46nori/Z80Atmega128/schematics/KiCad/ExtIO_sch.kicad_sch

## KiCad design schematics/KiCad/ExtIO_sch.kicad_sch (2023-12-28, an earlier design)

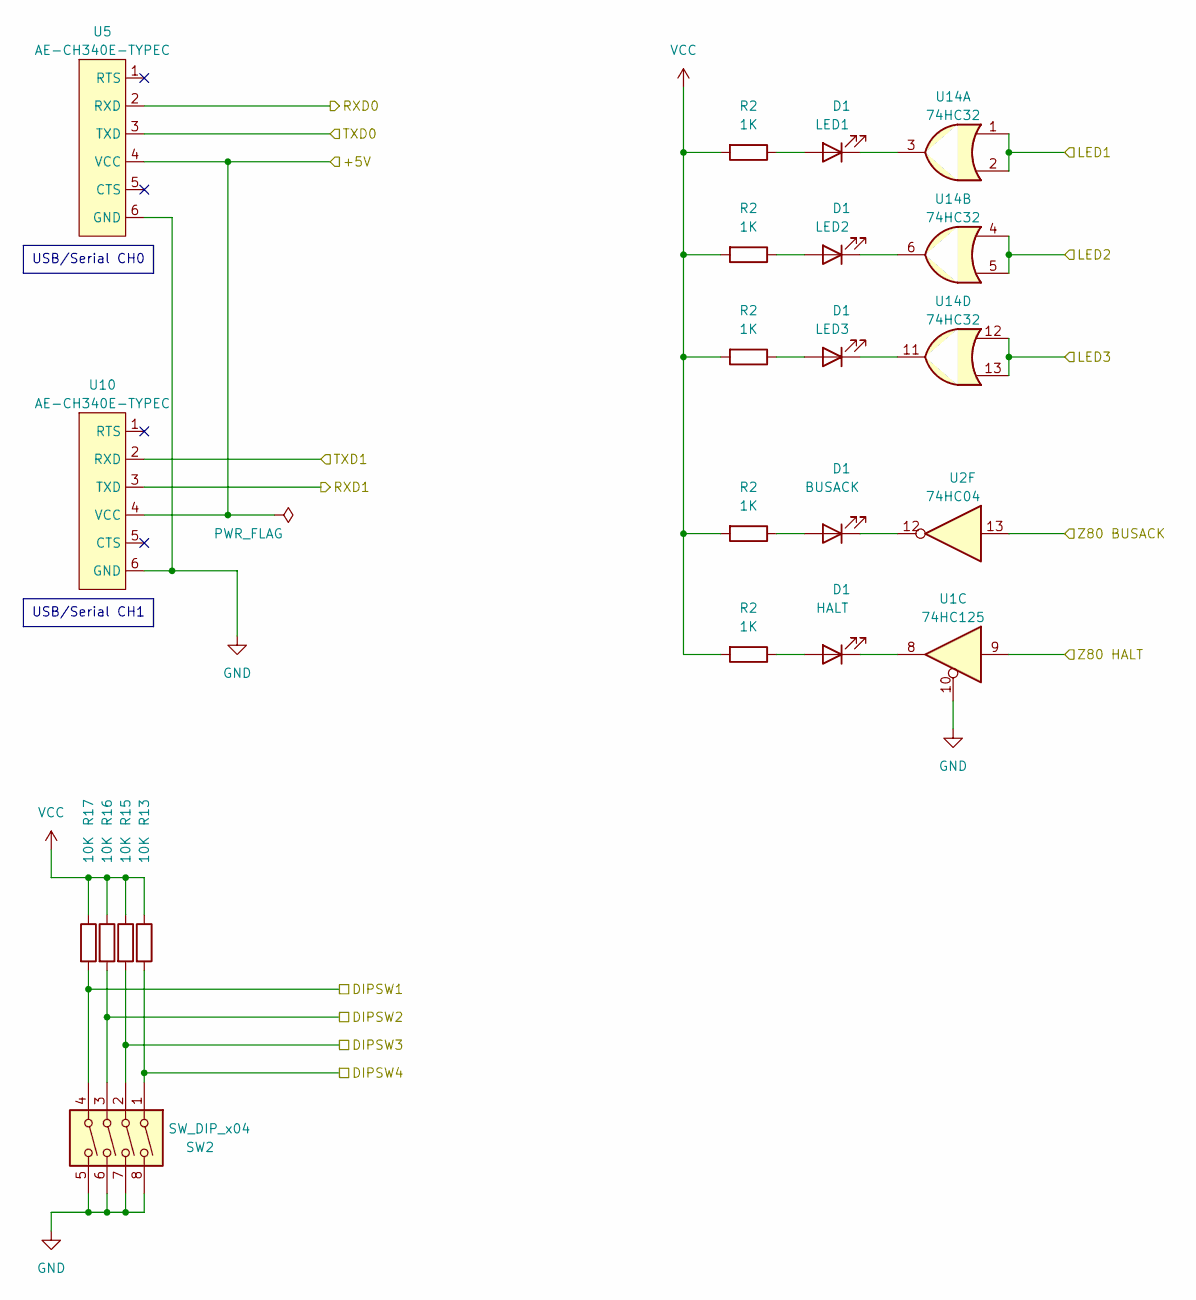
[picture p24: schematic ExtIO_sch.kicad_sch]

Parts:
D1: LED2; LED_D3.0mm
R2: 1K; R_Axial_DIN0204_L3.6mm_D1.6mm_P7.62mm_Horizontal
R13, R15, R16, R17: 10K; R_Axial_DIN0204_L3.6mm_D1.6mm_P7.62mm_Horizontal
SW2: SW_DIP_x04; SW_DIP_SPSTx04_Slide_9.78x12.34mm_W7.62mm_P2.54mm
U1: 74HC125; DIP-14_W7.62mm_Socket
U2: 74HC04; DIP-14_W7.62mm_Socket
U5, U10: AE-CH340E-TYPEC; PinHeader_1x06_P2.54mm_Vertical
U14: 74HC32; DIP-14_W7.62mm_Socket

Connections:
+5V: U5.4 (VCC), U10.4 (VCC)
DIPSW1: R17.2, SW2.4
DIPSW2: R16.2, SW2.3
DIPSW3: R15.2, SW2.2
DIPSW4: R13.2, SW2.1
GND: SW2.5, SW2.6, SW2.7, SW2.8, U1.10, U5.6 (GND), U10.6 (GND)
LED1: U14.1, U14.2
LED2: U14.4, U14.5
LED3: U14.12, U14.13
unnamed: D1.1 (K), U1.8, U2.12, U14.3, U14.6, U14.11
unnamed: D1.2 (A), R2.1
RXD0: U5.2 (RXD)
RXD1: U10.3 (TXD)
TXD0: U5.3 (TXD)
TXD1: U10.2 (RXD)
VCC: R2.2, R13.1, R15.1, R16.1, R17.1
Z80 BUSACK: U2.13
Z80 HALT: U1.9

Notes on the sheet:
USB/Serial CH1
USB/Serial CH0
