46nori/Z80Atmega128/schematics/KiCad/Reset.kicad_sch

## KiCad design schematics/KiCad/Reset.kicad_sch (2023-12-28, an earlier design)

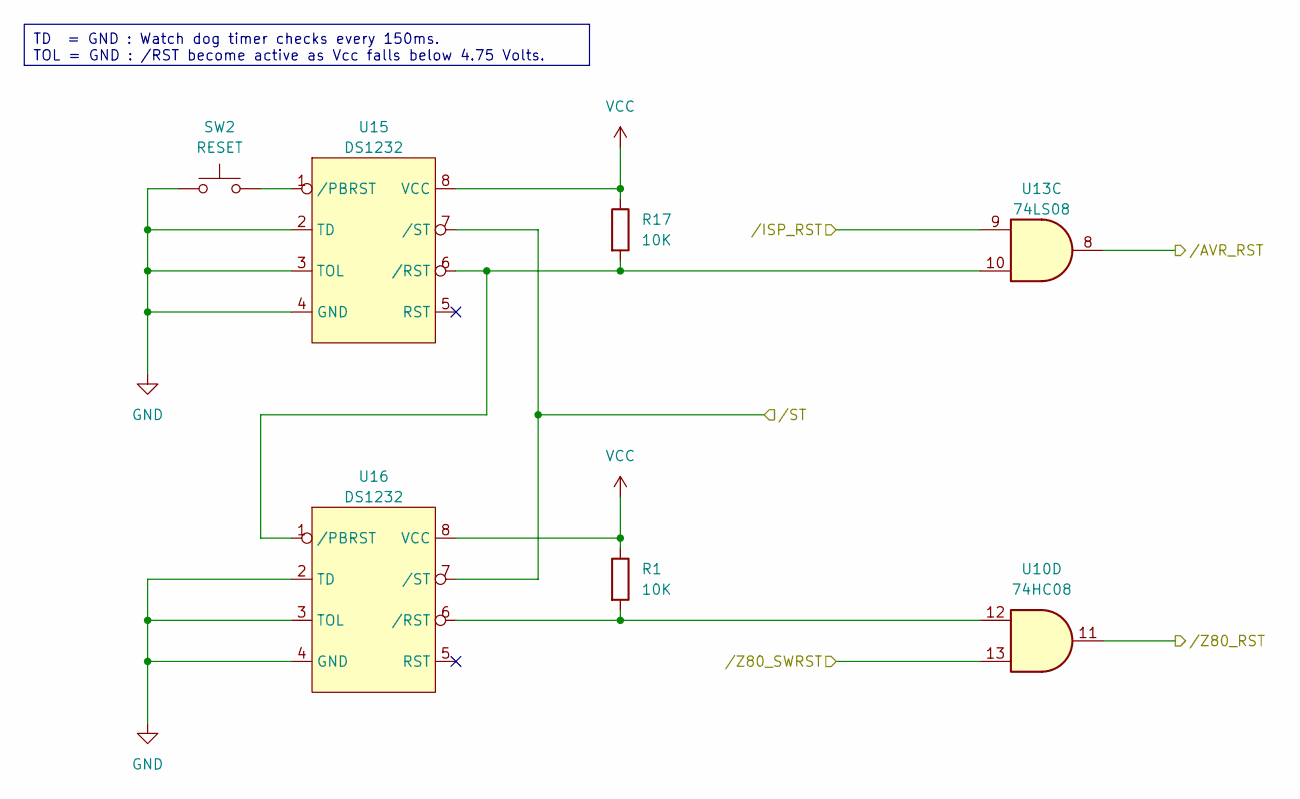
[picture p25: schematic Reset.kicad_sch]

Parts:
R1, R17: 10K; R_Axial_DIN0204_L3.6mm_D1.6mm_P7.62mm_Horizontal
SW2: RESET; SW_PUSH_6mm_H7.3mm
U10: 74HC08; DIP-14_W7.62mm_Socket
U13: 74LS08; DIP-14_W7.62mm_Socket
U15, U16: DS1232; DIP-8_W7.62mm

Connections:
GND: SW2.1, U15.2 (TD), U15.3 (TOL), U15.4 (GND), U16.2 (TD), U16.3 (TOL), U16.4 (GND)
unnamed: R1.2, U10.12, U16.6 (/RST)
unnamed: R17.2, U13.10, U15.6 (/RST), U16.1 (/PBRST)
unnamed: SW2.2, U15.1 (/PBRST)
VCC: R1.1, R17.1, U15.8 (VCC), U16.8 (VCC)
/AVR_RST: U13.8
/ISP_RST: U13.9
/ST: U15.7 (/ST), U16.7 (/ST)
/Z80_RST: U10.11
/Z80_SWRST: U10.13

Notes on the sheet:
TD = GND : Watch dog timer checks every 150ms. TOL = GND : /RST become active as Vcc falls below 4.75 Volts.
