46nori/Z80Atmega128/schematics/KiCad/SD_Card.kicad_sch

## KiCad design schematics/KiCad/SD_Card.kicad_sch (2023-12-28, an earlier design)

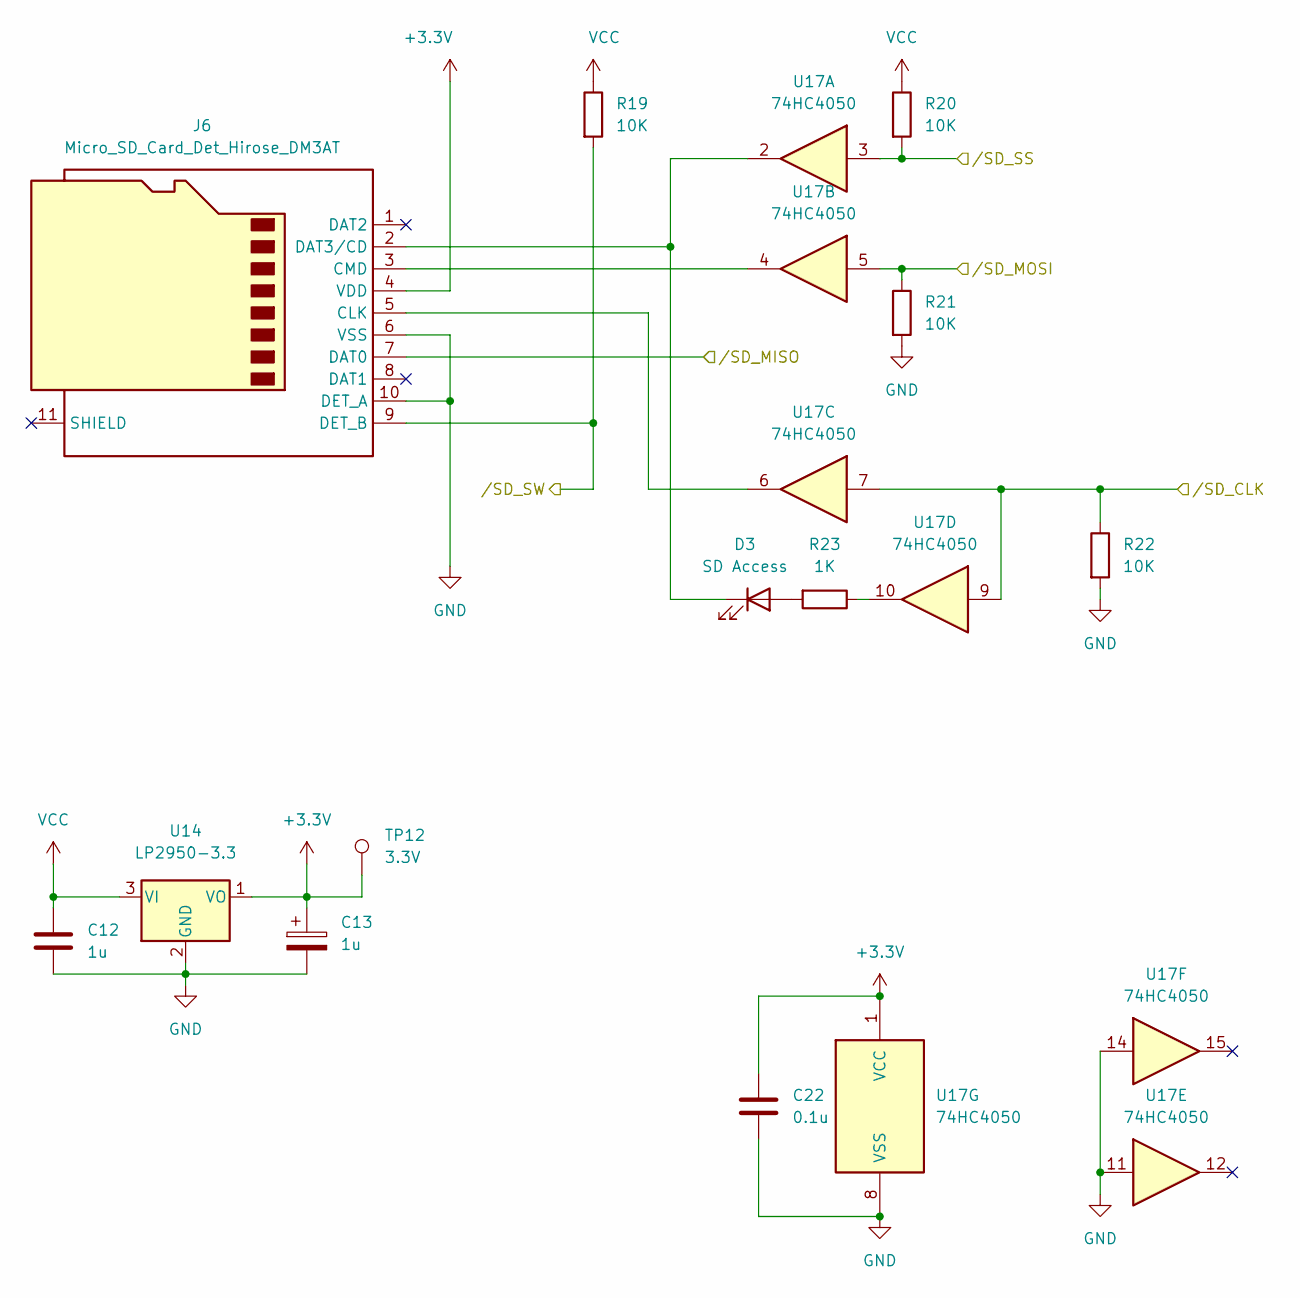
[picture p26: schematic SD_Card.kicad_sch]

Parts:
C12, C13: 1u; CP_Radial_Tantal_D5.0mm_P2.50mm
C22: 0.1u; C_Disc_D3.8mm_W2.6mm_P2.50mm
D3: SD Access; LED_D3.0mm
J6: Micro_SD_Card_Det_Hirose_DM3AT; microSD_HC_Hirose_DM3AT-SF-PEJM5
R19, R20, R21, R22: 10K; R_Axial_DIN0204_L3.6mm_D1.6mm_P7.62mm_Horizontal
R23: 1K; R_Axial_DIN0204_L3.6mm_D1.6mm_P7.62mm_Horizontal
TP12: 3.3V; TestPoint_Loop_D2.50mm_Drill1.0mm
U14: LP2950-3.3; TO-92_Inline
U17: 74HC4050; DIP-16_W7.62mm_Socket

Connections:
+3.3V: C13.1, C22.1, J6.4 (VDD), TP12.1, U14.1 (VO), U17.1 (VCC)
GND: C12.2, C13.2, C22.2, J6.6 (VSS), J6.10 (DET_A), R21.2, R22.2, U14.2 (GND), U17.8 (VSS), U17.11, U17.14
unnamed: D3.1 (K), J6.2 (DAT3/CD), U17.2
unnamed: D3.2 (A), R23.2
unnamed: J6.3 (CMD), U17.4
unnamed: J6.5 (CLK), U17.6
unnamed: R23.1, U17.10
VCC: C12.1, R19.1, R20.1, U14.3 (VI)
/SD_CLK: R22.1, U17.7, U17.9
/SD_MISO: J6.7 (DAT0)
/SD_MOSI: R21.1, U17.5
/SD_SS: R20.2, U17.3
/SD_SW: J6.9 (DET_B), R19.2
