46nori/Z80Atmega128/schematics/KiCad/Z80ATmega128.kicad_sch

## KiCad design schematics/KiCad/Z80ATmega128.kicad_sch (2023-12-28, an earlier design)

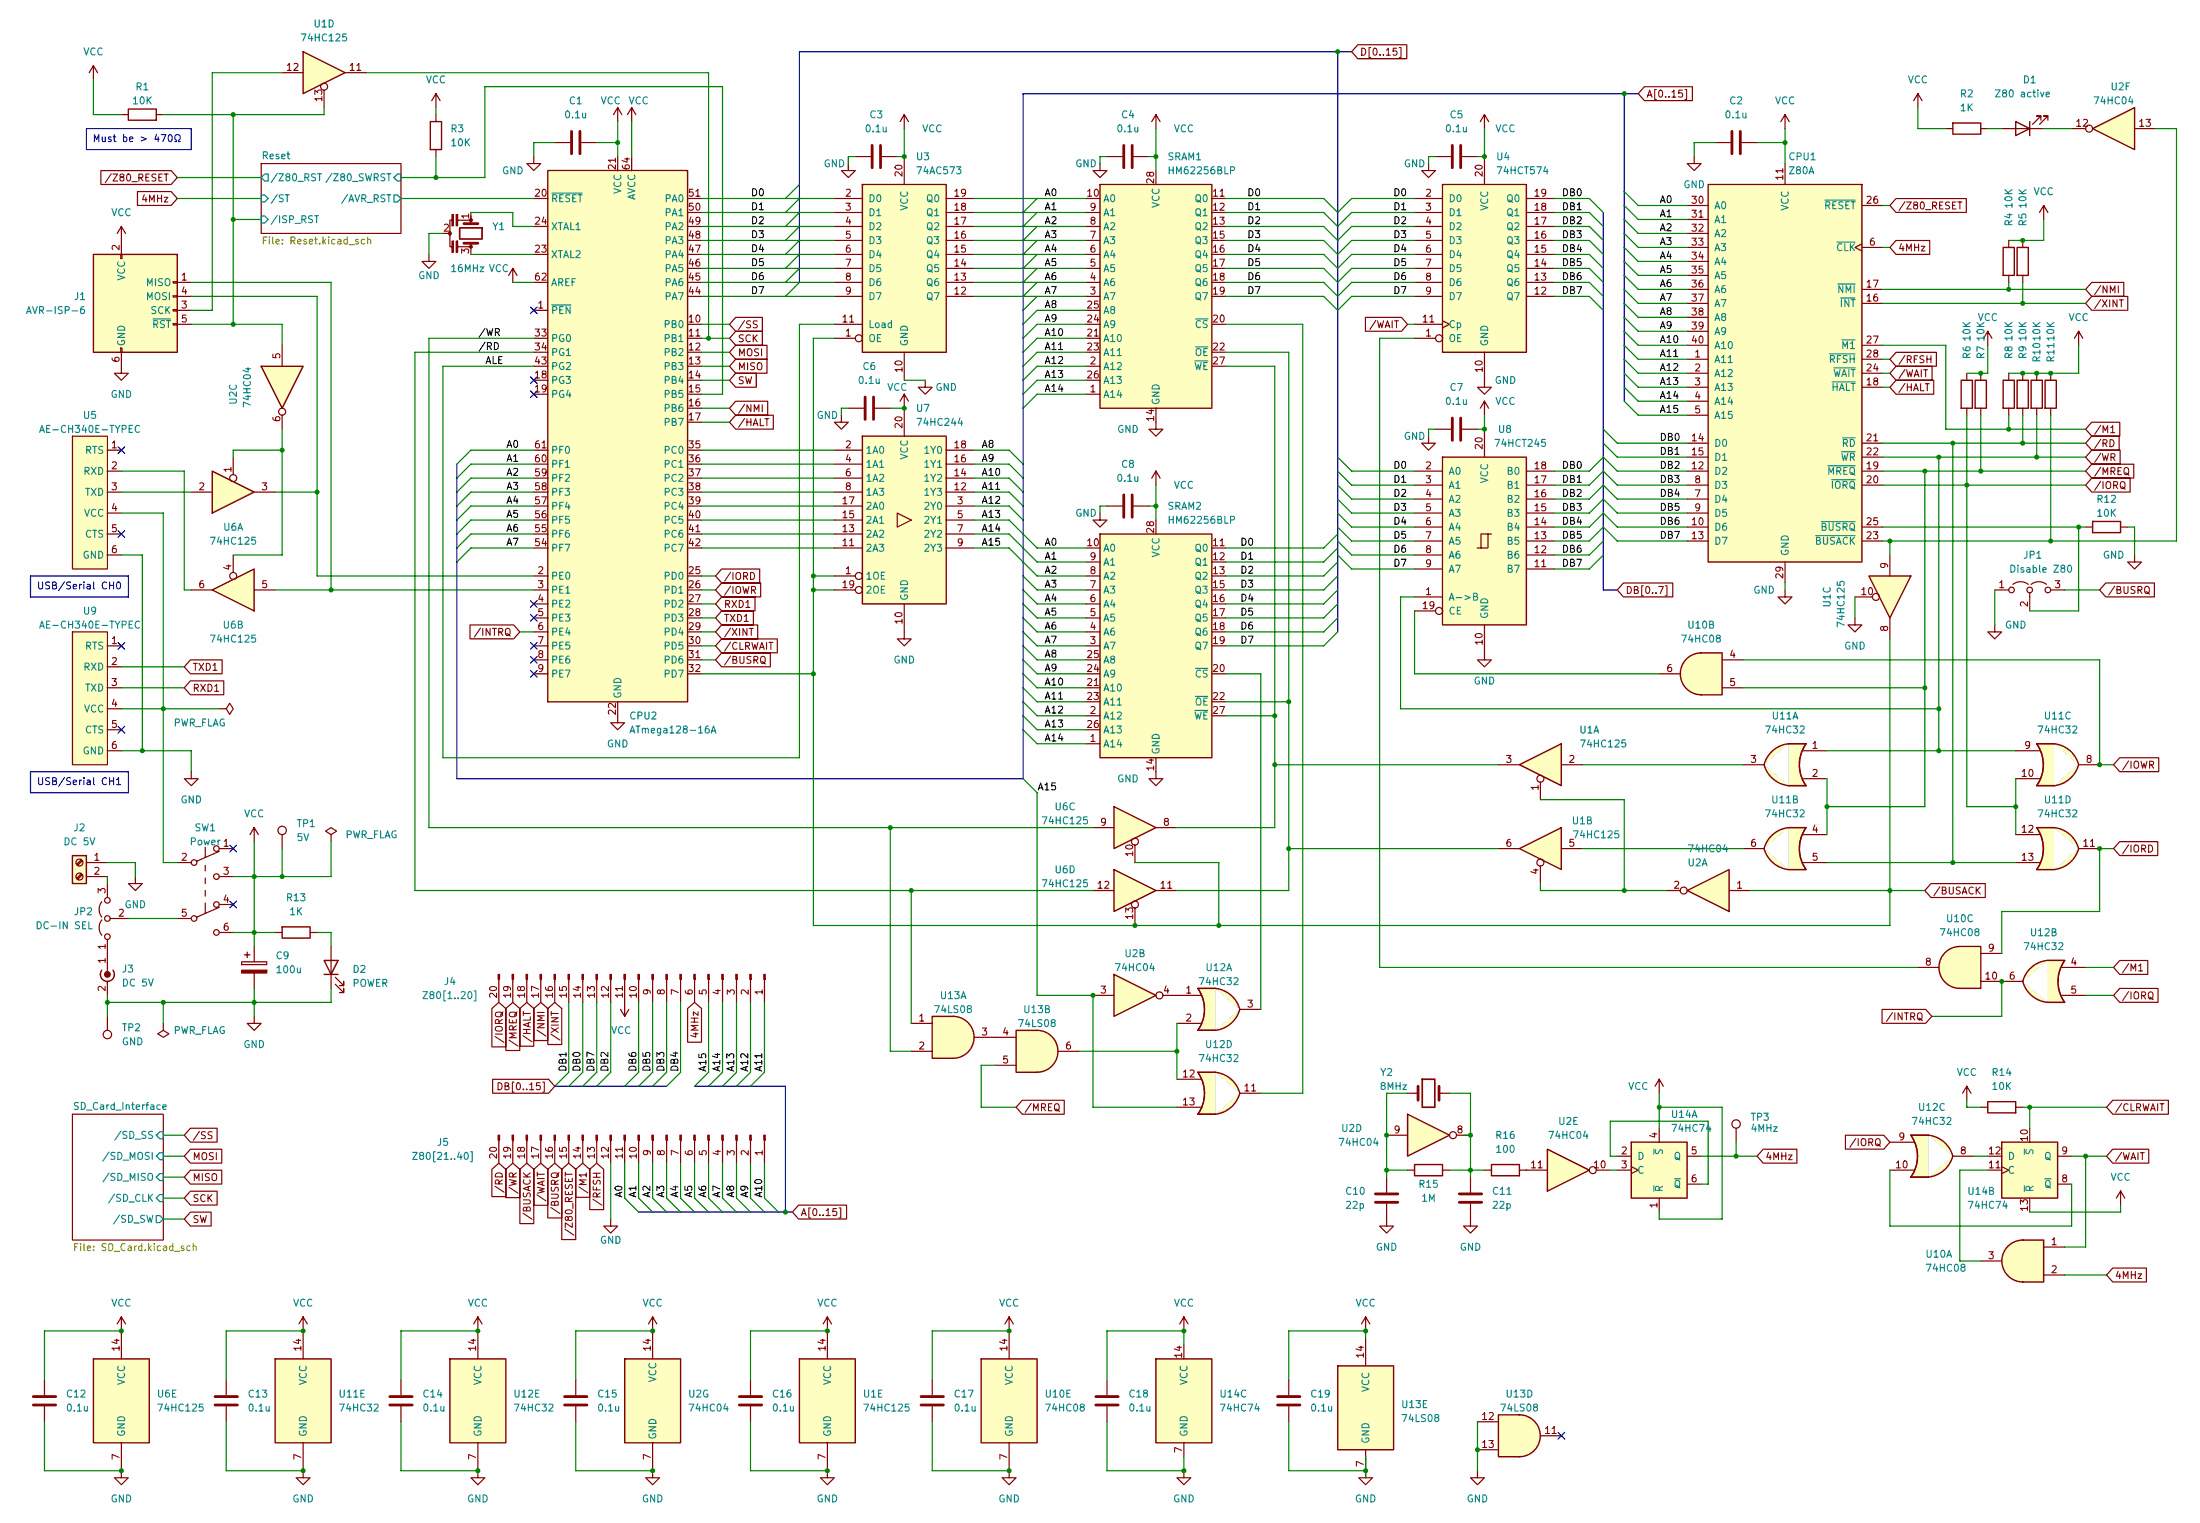
[picture p27: schematic Z80ATmega128.kicad_sch]

Parts:
C1, C2, C3, C4, C5, C6, C7, C8, C12, C13, C14, C15, C16, C17, C18, C19: 0.1u; C_Disc_D3.8mm_W2.6mm_P2.50mm
C9: 100u; CP_Radial_Tantal_D5.0mm_P2.50mm
C10, C11: 22p; C_Disc_D3.8mm_W2.6mm_P2.50mm
CPU1: Z80A; DIP-40_W15.24mm_Socket
CPU2: ATmega128-16A; TQFP-64_14x14mm_P0.8mm
D1: Z80 active; LED_D3.0mm
D2: POWER; LED_D3.0mm
J1: AVR-ISP-6; PinHeader_2x03_P2.54mm_Vertical
J2: DC 5V; TerminalBlock_Altech_AK300-2_P5.00mm
J3: DC 5V; BarrelJack_Horizontal
J4: Z80[1..20]; PinHeader_1x20_P2.54mm_Vertical
J5: Z80[21..40]; PinHeader_1x20_P2.54mm_Vertical
JP1: Disable Z80; PinHeader_1x03_P2.54mm_Vertical
JP2: DC-IN SEL; PinHeader_1x03_P2.54mm_Vertical
R1, R3, R4, R5, R6, R7, R8, R9, R10, R11, R12, R14: 10K; R_Axial_DIN0204_L3.6mm_D1.6mm_P7.62mm_Horizontal
R2, R13: 1K; R_Axial_DIN0204_L3.6mm_D1.6mm_P7.62mm_Horizontal
R15: 1M; R_Axial_DIN0204_L3.6mm_D1.6mm_P7.62mm_Horizontal
R16: 100; R_Axial_DIN0204_L3.6mm_D1.6mm_P7.62mm_Horizontal
SRAM1, SRAM2: HM62256BLP; DIP-28_W15.24mm_Socket
SW1: Power
TP1: 5V; TestPoint_Loop_D2.50mm_Drill1.0mm
TP2: GND; TestPoint_Loop_D2.50mm_Drill1.0mm
TP3: 4MHz; TestPoint_Loop_D2.50mm_Drill1.0mm
U1, U6: 74HC125; DIP-14_W7.62mm_Socket
U2: 74HC04; DIP-14_W7.62mm_Socket
U3: 74AC573; DIP-20_W7.62mm_Socket
U4: 74HCT574; DIP-20_W7.62mm_Socket
U5, U9: AE-CH340E-TYPEC; PinHeader_1x06_P2.54mm_Vertical
U7: 74HC244; DIP-20_W7.62mm_Socket
U8: 74HCT245; DIP-20_W7.62mm_Socket
U10: 74HC08; DIP-14_W7.62mm_Socket
U11, U12: 74HC32; DIP-14_W7.62mm_Socket
U13: 74LS08; DIP-14_W7.62mm_Socket
U14: 74HC74; DIP-14_W7.62mm_Socket
Y1: 16MHz; Resonator_Murata_CSTLSxxxX-3Pin_W5.5mm_H3.0mm
Y2: 8MHz; Crystal_HC18-U_Vertical

Connections:
4MHz: CPU1.6 (~CLK), J4.6, TP3.1, U10.2, U14.5 (Q)
A0: CPU1.30 (A0), CPU2.61 (PF0), J5.11, SRAM1.10 (A0), SRAM2.10 (A0), U3.19 (Q0)
A1: CPU1.31 (A1), CPU2.60 (PF1), J5.10, SRAM1.9 (A1), SRAM2.9 (A1), U3.18 (Q1)
A2: CPU1.32 (A2), CPU2.59 (PF2), J5.9, SRAM1.8 (A2), SRAM2.8 (A2), U3.17 (Q2)
A3: CPU1.33 (A3), CPU2.58 (PF3), J5.8, SRAM1.7 (A3), SRAM2.7 (A3), U3.16 (Q3)
A4: CPU1.34 (A4), CPU2.57 (PF4), J5.7, SRAM1.6 (A4), SRAM2.6 (A4), U3.15 (Q4)
A5: CPU1.35 (A5), CPU2.56 (PF5), J5.6, SRAM1.5 (A5), SRAM2.5 (A5), U3.14 (Q5)
A6: CPU1.36 (A6), CPU2.55 (PF6), J5.5, SRAM1.4 (A6), SRAM2.4 (A6), U3.13 (Q6)
A7: CPU1.37 (A7), CPU2.54 (PF7), J5.4, SRAM1.3 (A7), SRAM2.3 (A7), U3.12 (Q7)
A8: CPU1.38 (A8), J5.3, SRAM1.25 (A8), SRAM2.25 (A8), U7.18 (1Y0)
A9: CPU1.39 (A9), J5.2, SRAM1.24 (A9), SRAM2.24 (A9), U7.16 (1Y1)
A10: CPU1.40 (A10), J5.1, SRAM1.21 (A10), SRAM2.21 (A10), U7.14 (1Y2)
A11: CPU1.1 (A11), J4.1, SRAM1.23 (A11), SRAM2.23 (A11), U7.12 (1Y3)
A12: CPU1.2 (A12), J4.2, SRAM1.2 (A12), SRAM2.2 (A12), U7.3 (2Y0)
A13: CPU1.3 (A13), J4.3, SRAM1.26 (A13), SRAM2.26 (A13), U7.5 (2Y1)
A14: CPU1.4 (A14), J4.4, SRAM1.1 (A14), SRAM2.1 (A14), U7.7 (2Y2)
A15: CPU1.5 (A15), J4.5, U2.3, U7.9 (2Y3), U12.13
ALE: CPU2.43 (PG2), U3.11 (Load)
D0: CPU2.51 (PA0), SRAM1.11 (Q0), SRAM2.11 (Q0), U3.2 (D0), U4.2 (D0), U8.2 (A0)
D1: CPU2.50 (PA1), SRAM1.12 (Q1), SRAM2.12 (Q1), U3.3 (D1), U4.3 (D1), U8.3 (A1)
D2: CPU2.49 (PA2), SRAM1.13 (Q2), SRAM2.13 (Q2), U3.4 (D2), U4.4 (D2), U8.4 (A2)
D3: CPU2.48 (PA3), SRAM1.15 (Q3), SRAM2.15 (Q3), U3.5 (D3), U4.5 (D3), U8.5 (A3)
D4: CPU2.47 (PA4), SRAM1.16 (Q4), SRAM2.16 (Q4), U3.6 (D4), U4.6 (D4), U8.6 (A4)
D5: CPU2.46 (PA5), SRAM1.17 (Q5), SRAM2.17 (Q5), U3.7 (D5), U4.7 (D5), U8.7 (A5)
D6: CPU2.45 (PA6), SRAM1.18 (Q6), SRAM2.18 (Q6), U3.8 (D6), U4.8 (D6), U8.8 (A6)
D7: CPU2.44 (PA7), SRAM1.19 (Q7), SRAM2.19 (Q7), U3.9 (D7), U4.9 (D7), U8.9 (A7)
DB0: CPU1.14 (D0), J4.14, U4.19 (Q0), U8.18 (B0)
DB1: CPU1.15 (D1), J4.15, U4.18 (Q1), U8.17 (B1)
DB2: CPU1.12 (D2), J4.12, U4.17 (Q2), U8.16 (B2)
DB3: CPU1.8 (D3), J4.8, U4.16 (Q3), U8.15 (B3)
DB4: CPU1.7 (D4), J4.7, U4.15 (Q4), U8.14 (B4)
DB5: CPU1.9 (D5), J4.9, U4.14 (Q5), U8.13 (B5)
DB6: CPU1.10 (D6), J4.10, U4.13 (Q6), U8.12 (B6)
DB7: CPU1.13 (D7), J4.13, U4.12 (Q7), U8.11 (B7)
GND: C1.1, C2.1, C3.1, C4.1, C5.1, C6.1, C7.1, C8.1, C9.2, C10.2, C11.2, C12.2, C13.2, C14.2, C15.2, C16.2, C17.2, C18.2, C19.2, CPU1.29 (GND), CPU2.22 (GND), CPU2.53 (GND), CPU2.63 (GND), D2.1 (K), J1.6 (GND), J2.1, J3.2 (Ext), J5.12, JP1.1 (A), R12.1, SRAM1.14 (GND), SRAM2.14 (GND), TP2.1, U1.7 (GND), U1.10, U2.7 (GND), U3.10 (GND), U4.10 (GND), U5.6 (GND), U6.7 (GND), U7.10 (GND), U8.10 (GND), U9.6 (GND), U10.7 (GND), U11.7 (GND), U12.7 (GND), U13.7 (GND), U13.12, U13.13, U14.7 (GND), Y1.2
MISO: CPU2.13 (PB3)
MOSI: CPU2.12 (PB2)
unnamed: C10.1, R15.2, U2.9, Y2.1
unnamed: C11.1, R15.1, R16.1, U2.8, Y2.2
unnamed: CPU1.23 (~BUSACK), R11.2, U1.9, U2.13
unnamed: CPU1.25 (~BUSRQ), JP1.2 (C), R12.2
unnamed: CPU2.2 (PE0), J1.4 (MOSI), U6.3
unnamed: CPU2.3 (PE1), J1.1 (MISO), U6.5
unnamed: CPU2.23 (XTAL2), Y1.3
unnamed: CPU2.24 (XTAL1), Y1.1
unnamed: CPU2.35 (PC0), U7.2 (1A0)
unnamed: CPU2.36 (PC1), U7.4 (1A1)
unnamed: CPU2.37 (PC2), U7.6 (1A2)
unnamed: CPU2.38 (PC3), U7.8 (1A3)
unnamed: CPU2.39 (PC4), U7.17 (2A0)
unnamed: CPU2.40 (PC5), U7.15 (2A1)
unnamed: CPU2.41 (PC6), U7.13 (2A2)
unnamed: CPU2.42 (PC7), U7.11 (2A3)
unnamed: D1.1 (K), U2.12
unnamed: D1.2 (A), R2.1
unnamed: D2.2 (A), R13.1
unnamed: J1.3 (SCK), U1.12
unnamed: J2.2, JP2.3 (B)
unnamed: J3.1 (In), JP2.1 (A)
unnamed: JP2.2 (C), SW1.5 (B)
unnamed: R16.2, U2.11
unnamed: SRAM1.20 (~CS), U12.11
unnamed: SRAM1.22 (~OE), SRAM2.22 (~OE), U1.6, U6.11
unnamed: SRAM1.27 (~WE), SRAM2.27 (~WE), U1.3, U6.8
unnamed: SRAM2.20 (~CS), U12.3
unnamed: SW1.2 (B), U5.4 (VCC), U9.4 (VCC)
unnamed: U1.1, U1.4, U2.2
unnamed: U1.2, U11.3
unnamed: U1.5, U11.6
unnamed: U2.6, U6.1, U6.4
unnamed: U5.2 (RXD), U6.6
unnamed: U5.3 (TXD), U6.2
unnamed: U10.3, U14.11 (C)
unnamed: U8.19 (CE), U10.6
unnamed: U4.1 (OE), U10.8
unnamed: U2.4, U12.1
unnamed: U12.8, U14.12 (D)
unnamed: U12.10, U14.8 (~Q)
unnamed: U12.2, U12.12, U13.6
unnamed: U13.3, U13.4
unnamed: U14.2 (D), U14.6 (~Q)
unnamed: U2.10, U14.3 (C)
RXD1: CPU2.27 (PD2), U9.3 (TXD)
SCK: CPU2.11 (PB1), U1.11
SW: CPU2.14 (PB4)
TXD1: CPU2.28 (PD3), U9.2 (RXD)
VCC: C1.2, C2.2, C3.2, C4.2, C5.2, C6.2, C7.2, C8.2, C9.1, C12.1, C13.1, C14.1, C15.1, C16.1, C17.1, C18.1, C19.1, CPU1.11 (VCC), CPU2.21 (VCC), CPU2.52 (VCC), CPU2.62 (AREF), CPU2.64 (AVCC), J1.2 (VCC), J4.11, R1.1, R2.2, R3.1, R4.1, R5.1, R6.1, R7.1, R8.1, R9.1, R10.1, R11.1, R13.2, R14.1, SRAM1.28 (VCC), SRAM2.28 (VCC), SW1.3 (C), SW1.6 (C), TP1.1, U1.14 (VCC), U2.14 (VCC), U3.20 (VCC), U4.20 (VCC), U6.14 (VCC), U7.20 (VCC), U8.20 (VCC), U10.14 (VCC), U11.14 (VCC), U12.14 (VCC), U13.14 (VCC), U14.1 (~R), U14.4 (~S), U14.13 (~R), U14.14 (VCC)
/AVR_RST: CPU2.20 (~RESET)
/BUSACK: CPU2.32 (PD7), J5.18, U1.8, U2.1, U3.1 (OE), U6.10, U6.13, U7.1 (1OE), U7.19 (2OE)
/BUSRQ: CPU2.31 (PD6), J5.16, JP1.3 (B)
/CLRWAIT: CPU2.30 (PD5), R14.2, U14.10 (~S)
/HALT: CPU1.18 (~HALT), CPU2.17 (PB7), J4.18
/INTRQ: CPU2.6 (PE4), U10.10, U12.6
/IORD: CPU2.25 (PD0), U10.9, U11.11
/IORQ: CPU1.20 (~IORQ), J4.20, R6.2, U11.10, U11.12, U12.5, U12.9
/IOWR: CPU2.26 (PD1), U10.4, U11.8
/ISP_RST: J1.5 (~RST), R1.2, U1.13, U2.5
/M1: CPU1.27 (~M1), J5.14, R8.2, U12.4
/MREQ: CPU1.19 (~MREQ), J4.19, R7.2, U10.5, U11.2, U11.4, U13.5
/NMI: CPU1.17 (~NMI), CPU2.16 (PB6), J4.17, R4.2
/RD: CPU1.21 (~RD), CPU2.34 (PG1), J5.20, R9.2, U6.12, U11.5, U11.13, U13.1
/RFSH: CPU1.28 (~RFSH), J5.13
/SS: CPU2.10 (PB0)
/WAIT: CPU1.24 (~WAIT), J5.17, U4.11 (Cp), U10.1, U14.9 (Q)
/WR: CPU1.22 (~WR), CPU2.33 (PG0), J5.19, R10.2, U6.9, U8.1 (A->B), U11.1, U11.9, U13.2
/XINT: CPU1.16 (~INT), CPU2.29 (PD4), J4.16, R5.2
/Z80_RESET: CPU1.26 (~RESET), J5.15
/Z80_SWRST: CPU2.15 (PB5), R3.2

Notes on the sheet:
Must be > 470Ω
USB/Serial CH0
USB/Serial CH1
