46nori/Z80Atmega128/avr/src/z80io.c

/*
 * z80io.c
 *
 * Created: 2023/04/07 21:44:00
 *  Author: 46nori
 */ 
#include "z80io.h"
#include "xconsoleio.h"

//
// Initialize external memory settings
//
void ExtMem_Init(int wait)
{
	// WAIT setting for external SRAM
	if (wait < 2) {
		// SRAM access time < 100ns
		SET_BIT(MCUCR, SRW10);					// 1wait(SRW10=1)
		SET_BYTE(XMCRA, _BV(SRW00));			// 1wait(SRW0x=01, SRW11=0)
	} else {
		// SRAM access time >= 100ns
		CLR_BIT(MCUCR, SRW10);					// 2wait(SRW10=0)
		SET_BYTE(XMCRA, _BV(SRW01)|_BV(SRW11));	// 2wait(SRW0x=10, SRW11=1)
	}
	SET_BYTE(XMCRB, 0x00);		// Disable external memory bus-keeper
	
	SET_BYTE(PORTA, 0xff);		// Set PORTA as Hi-Z
	SET_BYTE(DDRA,  0x00);		//
	SET_BYTE(PORTC, 0x00);		// Force higher address disable
	SET_BYTE(DDRC,  0xff);		// Set PORTC as output
}

//
// Attach external memory and make Z80 suspend
// Caution: Do NOT call at the interrupt handler
//          for Z80 (/IN0, /INT1, /INT4)
//
void ExtMem_attach(void)
{
	Z80_BUSREQ(1);				// Acquire memory bus
	SET_BIT(MCUCR, SRE);		// Enable XMEM
}

//
// Detach external memory and let Z80 be active
//
void ExtMem_detach(void)
{
	CLR_BIT(MCUCR, SRE);		// Disable XMEM
	Z80_BUSREQ(0);				// Release memory bus
}

//
// Set shadow area to access hiding area of external memory
//
void *ExtMem_map(void)
{
	SET_BYTE(XMCRB, 0x03);	// Enable shadow
	return (void *)0x2000;
}

void ExtMem_unmap(void)
{
	SET_BYTE(XMCRB, 0x00);	// Disable shadow
}

//
// Z80 control
//
//
// Invoke /BUSRQ (PD6)
//
void Z80_BUSREQ(int st)
{
	if (st) {
		// Enable /BUSREQ
		CLR_BIT(PORTD, PORTD6);
		// Wait for /BUSACK
		while (PIND & _BV(PORTD7)) {
			//x_putchar('#');		// debug
		}
	} else {
		// Disable /BUSREQ
		SET_BIT(PORTD, PORTD6);
	}
}

//
// Invoke /RESET (PB5) to reset Z80
//
void Z80_RESET(void)
{
	ExtMem_detach();
	// Send reset pulse
	CLR_BIT(PORTB, PORTB5);
	_delay_ms(10);
	SET_BIT(PORTB, PORTB5);
}

//
// Invoke /NMI (PB6) for Z80 NMI
//   /NMI required >80ns low period in Z80A
void Z80_NMI(void)
{
	CLR_BIT(PORTB, PORTB6);		// t_w(/NML) > 80ns
	asm("NOP");					// 62.5ns (=1CLK@16MHz)
	asm("NOP");					// 62.5ns (=1CLK@16MHz)
	SET_BIT(PORTB, PORTB6);	
}

//
// Reset Z80 and go to specified address 
//   adr is jump address
//   0x0000-0x0003 is overwritten with 'JP adr'.
//
void Z80_RESET_GO(uint8_t *adr)
{
	SET_BIT(MCUCR, SRE);		// Enable XMEM
	uint8_t *p = (uint8_t *)ExtMem_map();	// 0x0000
	p[0] = 0xc3;							// JP
	p[1] = (uint16_t)adr & 0xff;			// Low address
	p[2] = ((uint16_t)adr >> 8) & 0xff;		// High address
	ExtMem_unmap();
	CLR_BIT(MCUCR, SRE);		// Disable XMEM
	Z80_RESET();
}

//
// Invoke /XINT (PD4) for Z80 INT
//
// vector should be set as following:
//   Mode2 : interrupt number * 2
//           e.g., 16 should be set in case of INT8
//   Mode0 : Z80 instruction
//

volatile uint8_t z80_int_vector;

//
// Interrupt vector FIFO queue
//
#define INT_QUEUE_SIZE 8
static volatile uint8_t int_queue[INT_QUEUE_SIZE];
static volatile uint8_t int_queue_head = 0;
static volatile uint8_t int_queue_tail = 0;

void Z80_EXTINT_low(uint8_t vector)
{
	z80_int_vector = vector;
	CLR_BIT(PORTD, PORTD4);		// /INT = Low
}

void Z80_EXTINT_High(void)
{
	SET_BIT(PORTD, PORTD4);		// /INT = High
}

void Z80_EXTINT_enqueue(uint8_t vector)
{
	uint8_t sreg = SREG;
	cli();
	uint8_t next = (int_queue_tail + 1) % INT_QUEUE_SIZE;
	if (next != int_queue_head) {
		int_queue[int_queue_tail] = vector;
		int_queue_tail = next;
	}
	// Assert /INT only when queue transitions from empty (count == 1)
	uint8_t count = (int_queue_tail - int_queue_head + INT_QUEUE_SIZE) % INT_QUEUE_SIZE;
	if (count == 1) {
		z80_int_vector = vector;
		CLR_BIT(PORTD, PORTD4);		// /INT = Low
	}
	SREG = sreg;
}

uint8_t Z80_EXTINT_dequeue(void)
{
	if (int_queue_head == int_queue_tail) {
		return 0;	// queue empty
	}
	int_queue_head = (int_queue_head + 1) % INT_QUEUE_SIZE;
	if (int_queue_head != int_queue_tail) {
		z80_int_vector = int_queue[int_queue_head];
		return 1;	// more entries remain
	}
	return 0;	// queue now empty
}

void Z80_EXTINT(uint8_t vector)
{
	Z80_EXTINT_low(vector);		// /INT = Low
	_delay_us(1);				// t_s(IT) > 80ns
	Z80_EXTINT_High();			// /INT = High
}

//
// Clear /CLRWAIT (PD5) to deactivate Z80 /WAIT
// Pulse width must be >250ns (Z80 1CLK@4MHz)
//   62.5ns(AVR 1CLK@16MHz) * 5CLK = 312.5ns
void Z80_CLRWAIT(void)
{
	CLR_BIT(PORTD, PORTD5);
	asm("NOP");					// 1 CLK
	asm("NOP");					// 1 CLK
	asm("NOP");					// 1 CLK
	SET_BIT(PORTD, PORTD5);		// 2 CLK
}

//
// Set HALT instruction at 0x0000 to stay Z80 halt after reset
//
void Z80_HALT(void)
{
	SET_BIT(MCUCR, SRE);		// Enable XMEM
	*(volatile uint8_t *)ExtMem_map() = 0x76;	// HALT instruction
	ExtMem_unmap();
	CLR_BIT(MCUCR, SRE);		// Disable XMEM
}

//
// Sense Z80 /BUSRQ
//   return 0(Low), 1(High)
//
int Is_Z80_BUSRQ(void)
{
	return PIND & _BV(PORTD6) ? 1 : 0;
}

//
// Sense Z80 /BUSACK
//   return 0(Low), 1(High)
//
int Is_Z80_BUSACK(void)
{
	return PIND & _BV(PORTD7) ? 1 : 0;
}

//
// Sense Z80 /HALT
//   return 0(Low), 1(High)
//
int Is_Z80_HALT(void)
{
	return PINB & _BV(PORTB7) ? 1 : 0;
}
