46nori/Z80Atmega128/avr/src/timer.h

/*
 * timer.h
 *
 * Created: 2023/06/11 21:56:52
 *  Author: 46nori
 */ 

#ifndef TIMER_H_
#define TIMER_H_
#include <asf.h>

void Timer0_Init(unsigned int n);
void Timer2_Init(unsigned int n);

#endif /* TIMER_H_ */
