46nori/Z80Atmega128/avr/src/usart.c

/*
 * usart.c
 *
 * Created: 2023/03/31 17:41:05
 *  Author: 46nori
 */ 
#include "usart.h"

void USART0_Init(uint32_t baud)
{
	// Set baud rate
	uint16_t br = FOSC / 16 / (baud - 1);
	UBRR0H = (uint8_t)((br>>8) & 0x0f);	// High byte
	UBRR0L = (uint8_t)(br & 0xff);		// Low byte
	// Set frame settings : async, 8bit, non-parity, 1 stop bit
	UCSR0C = _BV(UCSZ01)|_BV(UCSZ00);
	// Enable RX1 and TX1
	UCSR0B = 0;				// discard unread data in fifo
	UCSR0B = _BV(RXEN0) | _BV(TXEN0);
}

void USART1_Init(uint32_t baud)
{
	// Set baud rate
	uint16_t br = FOSC / 16 / (baud - 1);
	UBRR1H = (uint8_t)((br>>8) & 0x0f);	// High byte
	UBRR1L = (uint8_t)(br & 0xff);		// Low byte
	// Set frame settings : async, 8bit, non-parity, 1 stop bit
	UCSR1C = _BV(UCSZ11)|_BV(UCSZ10);
	// Enable RX1(and interrupt) and TX1
	UCSR1B = 0;				// discard unread data in fifo
	UCSR1B = _BV(RXEN1) | _BV(TXEN1) | _BV(RXCIE1);;
}

void USART0_Transmit(uint8_t data)
{
	while (!(UCSR0A & _BV(UDRE0)));
	UDR0 = data;
}

void USART1_Transmit(uint8_t data)
{
	while (!(UCSR1A & _BV(UDRE1)));
	UDR1 = data;
}

uint8_t USART0_Receive(void)
{
	while (!(UCSR0A & _BV(RXC0)));
	return UDR0;
}

int USART0_Receive_tout(uint32_t us)
{
	if (us == 0) {
		return USART0_Receive();
	}
	while (us--) {
		if (UCSR0A & _BV(RXC0)) {
			return UDR0;
		}
		_delay_us(1);
	}	
	return EOF;
}

uint8_t USART1_Receive(void)
{
	while (!(UCSR1A & _BV(RXC1)));
	return UDR1;
}
